felipericobello/PhotoWebBluetooth32-hardware/images/Photogate_render2.png

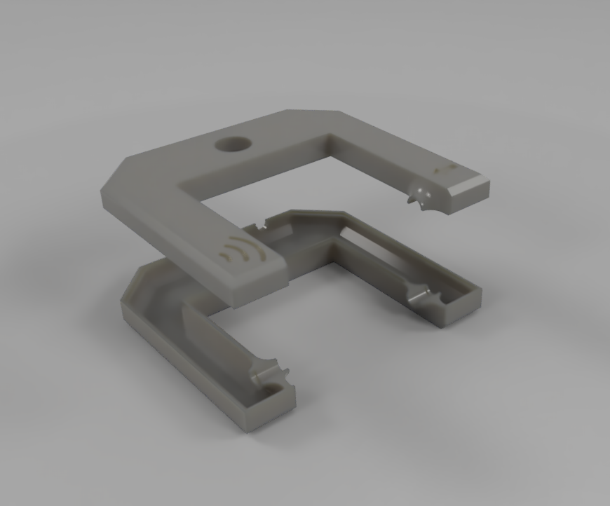
images/Photogate_render2.png
