felipericobello/PhotoWebBluetooth32-hardware/images/Photogate_render3.png

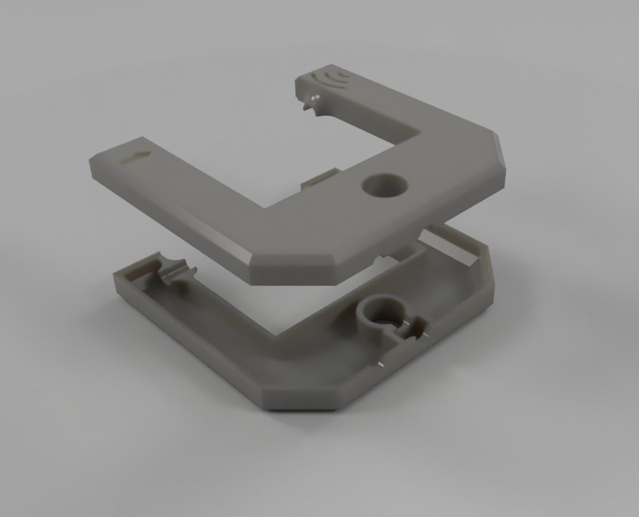
images/Photogate_render3.png
