felipericobello/PhotoWebBluetooth32-hardware/PCB/images/PCB.png

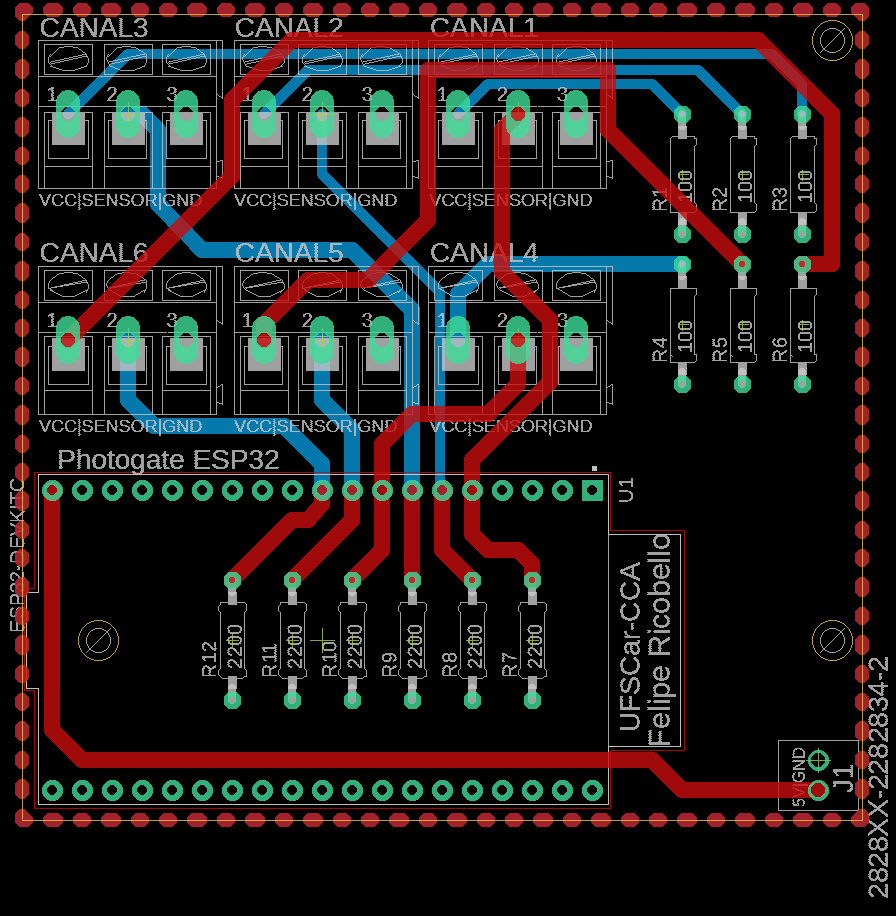
PCB/images/PCB.png
